lairdrt/yolink-thermometer-cradle/photos/IMG_7471.jpg

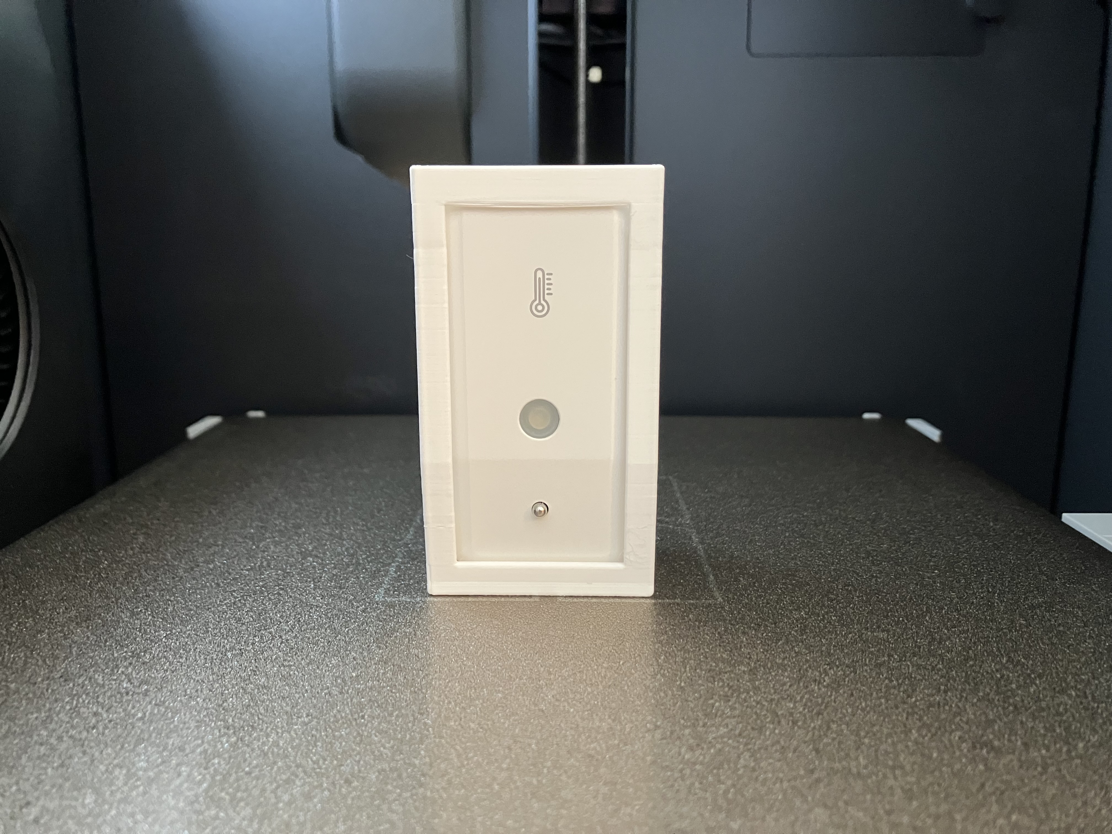
photos/IMG_7471.jpg
