lairdrt/yolink-thermometer-cradle/photos/IMG_7473.jpg

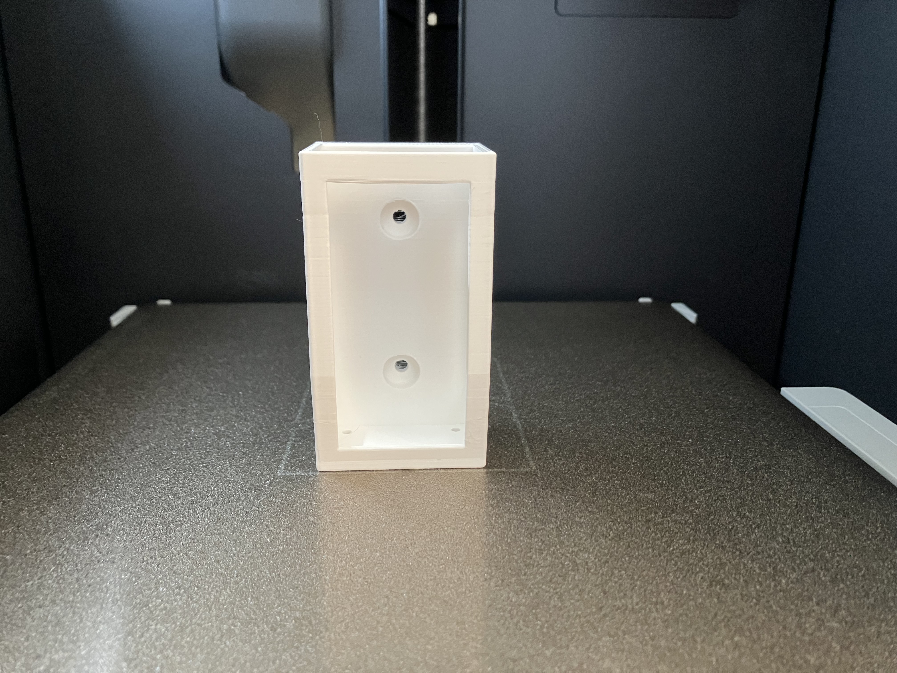
photos/IMG_7473.jpg
