lairdrt/yolink-thermometer-cradle/photos/IMG_7474.jpg

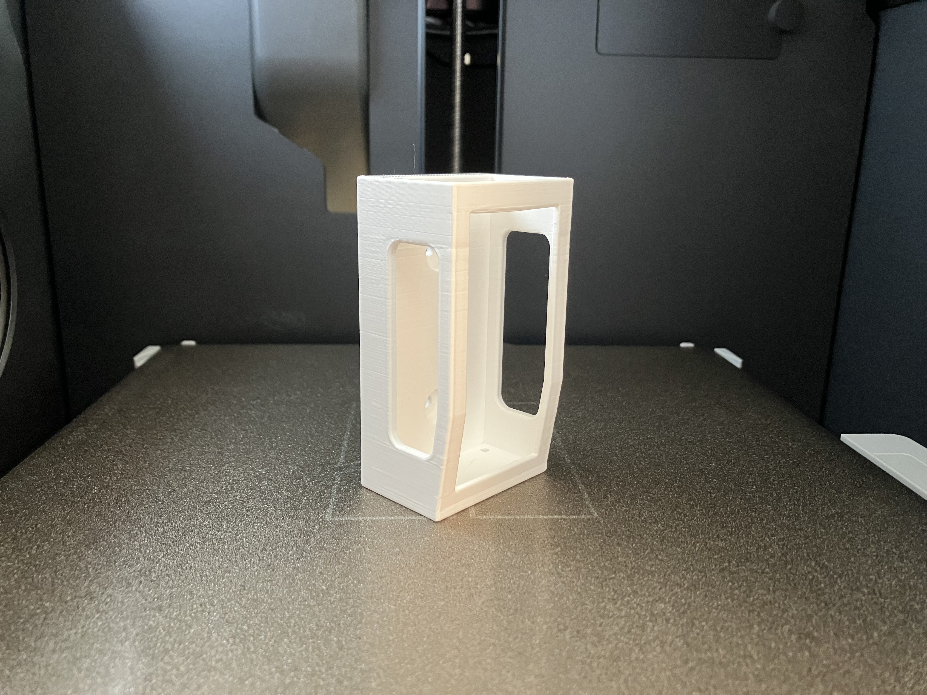
photos/IMG_7474.jpg
