lairdrt/yolink-thermometer-cradle/photos/IMG_7475.jpg

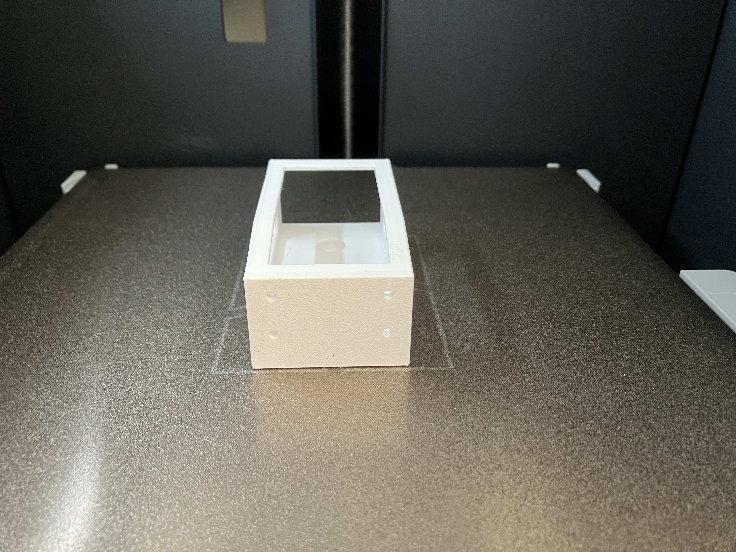
photos/IMG_7475.jpg
