lairdrt/yolink-thermometer-cradle/photos/IMG_7477.jpg

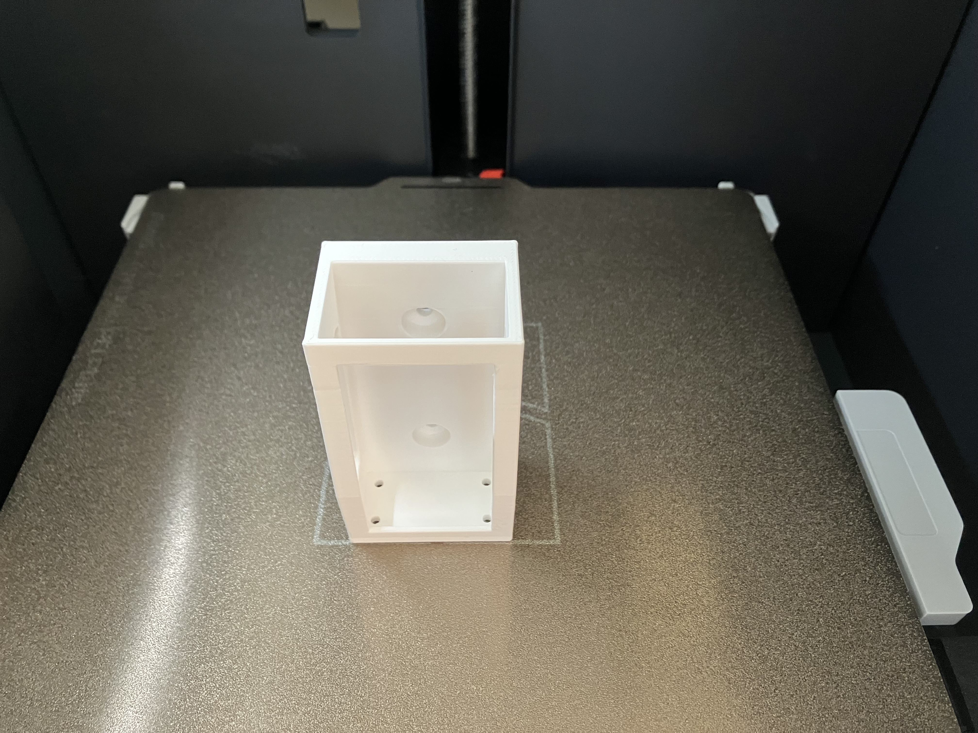
photos/IMG_7477.jpg
