lairdrt/yolink-thermometer-cradle/photos/IMG_7481.jpg

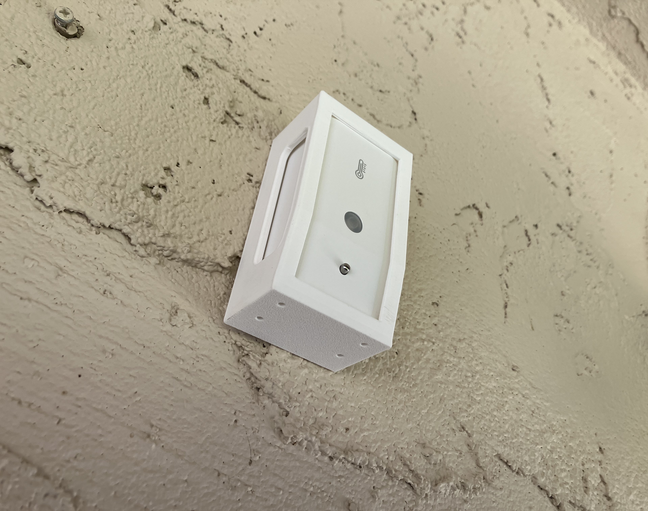
photos/IMG_7481.jpg
